kpatrykEIT/DDS_generator_ATmega32u4/Program/sawtooth_wave.h

#ifndef SAWTOOTH_WAVE_H
#define SAWTOOTH_WAVE_H

#include <stdint.h>

const uint8_t sawtooth_wave[1024] = {
    0,   0,   0,   0,   0,   1,   1,   1,   1,   2,   2,   2,   2,   3,   3,   3,
    3,   4,   4,   4,   4,   5,   5,   5,   5,   6,   6,   6,   6,   7,   7,   7,
    7,   8,   8,   8,   8,   9,   9,   9,   9,  10,  10,  10,  10,  11,  11,  11,
   11,  12,  12,  12,  12,  13,  13,  13,  13,  14,  14,  14,  14,  15,  15,  15,
   15,  16,  16,  16,  16,  17,  17,  17,  17,  18,  18,  18,  18,  19,  19,  19,
   19,  20,  20,  20,  20,  21,  21,  21,  21,  22,  22,  22,  22,  23,  23,  23,
   23,  24,  24,  24,  24,  25,  25,  25,  25,  26,  26,  26,  26,  27,  27,  27,
   27,  28,  28,  28,  28,  29,  29,  29,  29,  30,  30,  30,  30,  31,  31,  31,
   31,  32,  32,  32,  32,  33,  33,  33,  33,  34,  34,  34,  34,  35,  35,  35,
   35,  36,  36,  36,  36,  37,  37,  37,  37,  38,  38,  38,  38,  39,  39,  39,
   39,  40,  40,  40,  40,  41,  41,  41,  41,  42,  42,  42,  42,  43,  43,  43,
   43,  44,  44,  44,  44,  45,  45,  45,  45,  46,  46,  46,  46,  47,  47,  47,
   47,  48,  48,  48,  48,  49,  49,  49,  49,  50,  50,  50,  50,  51,  51,  51,
   51,  52,  52,  52,  52,  53,  53,  53,  53,  54,  54,  54,  54,  55,  55,  55,
   55,  56,  56,  56,  56,  57,  57,  57,  57,  58,  58,  58,  58,  59,  59,  59,
   59,  60,  60,  60,  60,  61,  61,  61,  61,  62,  62,  62,  62,  63,  63,  63,
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
	192,193,194,195,196,197,198,199,200,201,202,203,204,205,206,207,
	208,209,210,211,212,213,214,215,216,217,218,219,220,221,222,223,
	224,225,226,227,228,229,230,231,232,233,234,235,236,237,238,239,
	240,241,242,243,244,245,246,247,248,249,250,251,252,253,254,255
};

#endif // SAWTOOTH_WAVE_H
