kpatrykEIT/DDS_generator_ATmega32u4/Program/sin_wave.h

#ifndef SIN_WAVE_H
#define SIN_WAVE_H

#include <stdint.h>

const uint8_t sin_wave[1024] = {
  127, 128, 129, 129, 130, 131, 132, 132, 133, 134, 135, 136, 136, 137, 138, 139,
  139, 140, 141, 142, 143, 143, 144, 145, 146, 146, 147, 148, 149, 150, 150, 151,
  152, 153, 153, 154, 155, 156, 156, 157, 158, 159, 159, 160, 161, 162, 163, 163,
  164, 165, 166, 166, 167, 168, 168, 169, 170, 171, 171, 172, 173, 174, 174, 175,
  176, 177, 177, 178, 179, 179, 180, 181, 182, 182, 183, 184, 184, 185, 186, 186,
  187, 188, 188, 189, 190, 191, 191, 192, 193, 193, 194, 195, 195, 196, 197, 197,
  198, 198, 199, 200, 200, 201, 202, 202, 203, 204, 204, 205, 205, 206, 207, 207,
  208, 208, 209, 210, 210, 211, 211, 212, 213, 213, 214, 214, 215, 215, 216, 217,
  217, 218, 218, 219, 219, 220, 220, 221, 221, 222, 223, 223, 224, 224, 225, 225,
  226, 226, 227, 227, 228, 228, 228, 229, 229, 230, 230, 231, 231, 232, 232, 233,
  233, 233, 234, 234, 235, 235, 236, 236, 236, 237, 237, 238, 238, 238, 239, 239,
  239, 240, 240, 241, 241, 241, 242, 242, 242, 243, 243, 243, 244, 244, 244, 244,
  245, 245, 245, 246, 246, 246, 247, 247, 247, 247, 248, 248, 248, 248, 249, 249,
  249, 249, 249, 250, 250, 250, 250, 250, 251, 251, 251, 251, 251, 252, 252, 252,
  252, 252, 252, 252, 253, 253, 253, 253, 253, 253, 253, 253, 254, 254, 254, 254,
  254, 254, 254, 254, 254, 254, 254, 254, 254, 254, 254, 254, 254, 254, 254, 254,
  255, 254, 254, 254, 254, 254, 254, 254, 254, 254, 254, 254, 254, 254, 254, 254,
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
	0, 0, 0, 0, 1, 1, 1, 2,
	2, 3, 4, 5, 5, 6, 7, 9,
	10, 11, 12, 14, 15, 17, 18, 20,
	21, 23, 25, 27, 29, 31, 33, 35,
	37, 40, 42, 44, 47, 49, 52, 54,
	57, 59, 62, 65, 67, 70, 73, 76,
	79, 82, 85, 88, 90, 93, 97, 100,
103, 106, 109, 112, 115, 118, 121, 124};

#endif // SIN_WAVE_H
