kpatrykEIT/DDS_generator_ATmega32u4/Program/i2c_master.c

/*
* I2CMasterDevice.c
*
* Created: 12/9/2018 10:53:45 AM
*  Author: Denis Goriachev
*/

#ifndef  F_CPU
#define F_CPU 16000000UL
#endif

#include <avr/io.h>
#include <util/twi.h>
#include <stdint.h>

#include "i2c_master.h"

#define I2C_SCL_FREQUENCY_PRESCALER 1
#define I2C_TWBR_VALUE 

#define I2C_PRESCALER_MASK 0xF8

void i2c_master_init(unsigned long frequency)
{
	TWSR = 0;
	TWBR = (uint8_t)((((F_CPU / frequency) / I2C_SCL_FREQUENCY_PRESCALER) - 16 ) / 2);
	
}

uint8_t i2c_master_start(uint8_t address, uint8_t mode)
{
	uint8_t   twst;

	// reset control register
	TWCR = 0;

	// transmit START condition
	TWCR = (1<<TWINT) | (1<<TWSTA) | (1<<TWEN);
	
	// wait for end of transmission
	while( !(TWCR & (1<<TWINT)) );
	
	// check if the start condition was successfully transmitted. Mask prescaler bits.
	twst = TW_STATUS & I2C_PRESCALER_MASK;
	if ( (twst != TW_START) && (twst != TW_REP_START))
	{
		return I2C_STATUS_ERROR_START_WAS_NOT_ACCEPTED;
	}
	
	// load shifted slave address into data register with specified mode
	TWDR = (address << 1) | mode;

	// start transmission of address
	TWCR = (1<<TWINT) | (1<<TWEN);
	// wait for end of transmission
	while( !(TWCR & (1<<TWINT)) );
	
	// check if the device has acknowledged the READ / WRITE mode
	twst = TW_STATUS & I2C_PRESCALER_MASK;
	if ( (twst != TW_MT_SLA_ACK) && (twst != TW_MR_SLA_ACK) )
	{
		return I2C_STATUS_ERROR_TRANSMIT_OR_READ_WAS_NOT_ACKNOWLEDGED;
	}
	
	return I2C_STATUS_SUCCESS;
};

uint8_t i2c_master_startWait(uint8_t address, uint8_t mode)
{
	uint8_t twst;

	while (1)
	{
		// send START condition
		TWCR = (1<<TWINT) | (1<<TWSTA) | (1<<TWEN);
		// wait until transmission completed
		while(!(TWCR & (1<<TWINT)));
		
		// check value of TWI Status Register. Mask prescaler bits.
		twst = TW_STATUS & I2C_PRESCALER_MASK;
		if ( (twst != TW_START) && (twst != TW_REP_START)) continue;
		
		// send device address
		TWDR = (address << 1) | mode;
		TWCR = (1<<TWINT) | (1<<TWEN);
		// wail until transmission completed
		while(!(TWCR & (1<<TWINT)));
		
		// check value of TWI Status Register. Mask prescaler bits.
		twst = TW_STATUS & I2C_PRESCALER_MASK;
		if ( (twst == TW_MT_SLA_NACK )||(twst ==TW_MR_DATA_NACK) )
		{
			/* device busy, send stop condition to terminate write operation */
			TWCR = (1<<TWINT) | (1<<TWEN) | (1<<TWSTO);
			// wait until stop condition is executed and bus released
			while(TWCR & (1<<TWSTO));
			
			continue;
		}
		break;
	}

	return I2C_STATUS_SUCCESS;
};

uint8_t i2c_master_write(uint8_t data)
{
	uint8_t twst;

	// put data into data register
	TWDR = data;

	// start transmission of data
	TWCR = (1<<TWINT) | (1<<TWEN);
	// wait for end of transmission
	while( !(TWCR & (1<<TWINT)) );
	
	// check value of TWI Status Register. Mask prescaler bits
	twst = TW_STATUS & I2C_PRESCALER_MASK;

	// If Slave device not acknowledged transmission - returns an error
	if( twst != TW_MT_DATA_ACK)
	{
		return I2C_STATUS_ERROR_TRANSMIT_NOT_ACKNOWLEDGED;
	}
	
	return I2C_STATUS_SUCCESS;
}

uint8_t i2c_master_readAck(void)
{
	// start TWI module and acknowledge data after reception
	TWCR = (1<<TWINT) | (1<<TWEN) | (1<<TWEA);
	// wait for end of transmission
	while( !(TWCR & (1<<TWINT)) );

	return TWDR;
}

uint8_t i2c_master_readNack(void)
{
	// start receiving without acknowledging reception
	TWCR = (1<<TWINT) | (1<<TWEN);
	// wait for end of transmission
	while( !(TWCR & (1<<TWINT)) );

	// return received data from TWDR
	return TWDR;
}

uint8_t i2c_master_send(uint8_t address, uint8_t* data, uint16_t length)
{
	// starts the transmitting
	uint8_t status = i2c_master_start(address, I2C_WRITE);

	// in case of error - returns status code
	if (status) return status;
	
	for (uint16_t i = 0; i < length; i++)
	{
		status = i2c_master_write(data[i]);
		if (status) return status;
	}
	
	i2c_master_stop();
	
	return I2C_STATUS_SUCCESS;
}

uint8_t i2c_master_sendByte(uint8_t address, uint8_t data)
{
	uint8_t status = i2c_master_start(address, I2C_WRITE);
	if (status) return status;

	status = i2c_master_write(data);
	if (status) return status;

	i2c_master_stop();
	
	return I2C_STATUS_SUCCESS;
};

uint8_t i2c_master_receive(uint8_t address, uint8_t* data, uint16_t length)
{
	uint8_t status = i2c_master_start(address, I2C_READ);
	if (status) return status;
	
	for (uint16_t i = 0; i < (length-1); i++)
	{
		data[i] = i2c_master_readAck();
	}
	data[(length-1)] = i2c_master_readNack();
	
	i2c_master_stop();
	
	return I2C_STATUS_SUCCESS;
}



void i2c_master_stop(void)
{
	TWCR = (1<<TWINT) | (1<<TWEN) | (1<<TWSTO);
};
